BerretW/Project65/images/V9-1-2_Case.jpg

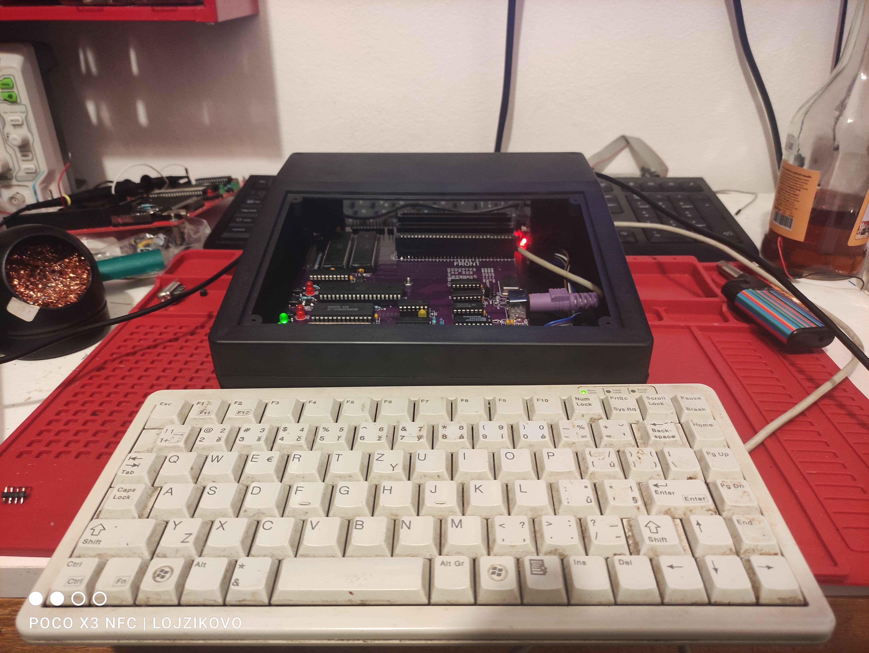
images/V9-1-2_Case.jpg
