BerretW/Project65/images/V9-1.jpg

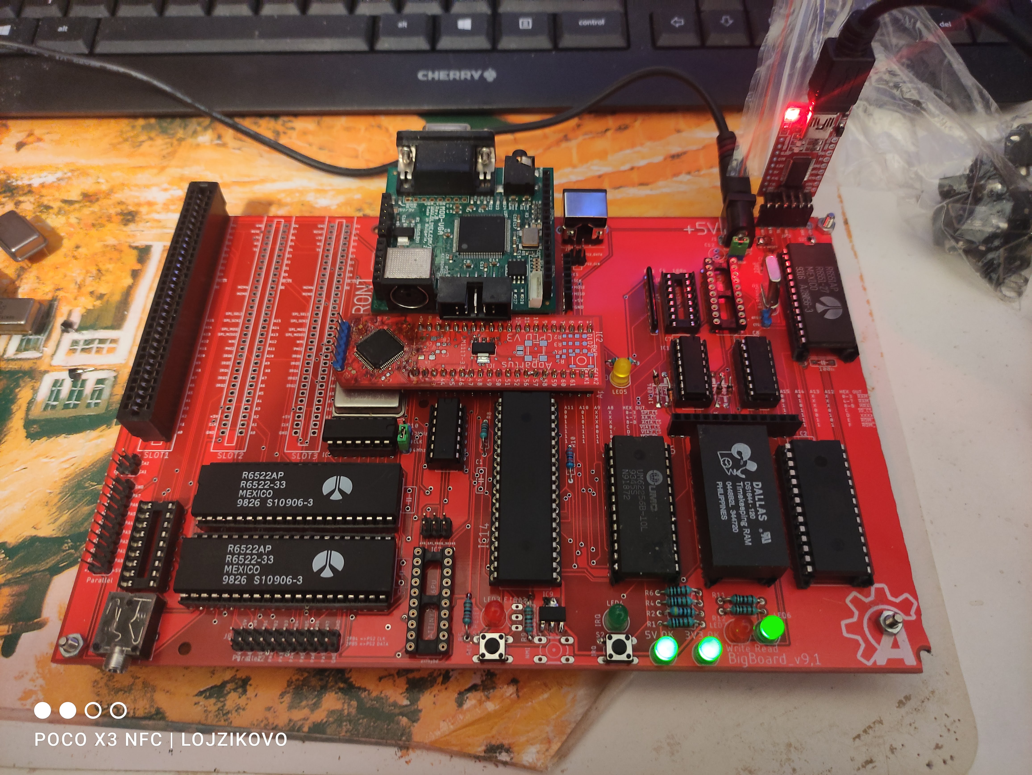
images/V9-1.jpg
